nigelfenton/shackswitch/hardwear/ant switch board.webp

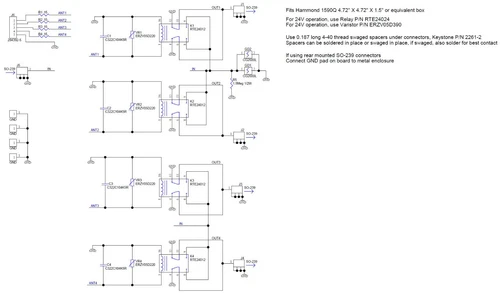
hardwear/ant switch board.webp
